cwilsonx100/FPGA-Synthesizer/Synth_V5_sequencer/fpga/Note_to_phase.v

`timescale 1ns / 1ps

//============================================================================
// Note_to_phase
//   MIDI note number -> 32-bit phase increment for the NCO.
//   Computed for Fs = 48000 Hz (clk_audio 12.288 MHz / 256), A4 = 440.000 Hz.
//   phase_inc = round( freq * 2^32 / Fs )
//============================================================================

module Note_to_phase(
    input  wire [6:0]  midi_note,
    output reg  [31:0] phase_inc
);

    always @(*) begin
        case (midi_note)

            7'd0:   phase_inc = 32'd731558;     // C-1   8.176 Hz
            7'd1:   phase_inc = 32'd775059;     // C#-1  8.662 Hz
            7'd2:   phase_inc = 32'd821146;     // D-1   9.177 Hz
            7'd3:   phase_inc = 32'd869974;     // D#-1  9.723 Hz
            7'd4:   phase_inc = 32'd921705;     // E-1   10.301 Hz
            7'd5:   phase_inc = 32'd976513;     // F-1   10.913 Hz
            7'd6:   phase_inc = 32'd1034579;    // F#-1  11.562 Hz
            7'd7:   phase_inc = 32'd1096099;    // G-1   12.250 Hz
            7'd8:   phase_inc = 32'd1161276;    // G#-1  12.978 Hz
            7'd9:   phase_inc = 32'd1230329;    // A-1   13.750 Hz
            7'd10:  phase_inc = 32'd1303488;    // A#-1  14.568 Hz
            7'd11:  phase_inc = 32'd1380998;    // B-1   15.434 Hz

            7'd12:  phase_inc = 32'd1463116;    // C0    16.352 Hz
            7'd13:  phase_inc = 32'd1550118;    // C#0   17.324 Hz
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
            7'd126: phase_inc = 32'd1059409297; // F#9   11839.822 Hz
            7'd127: phase_inc = 32'd1122405052; // G9    12543.854 Hz

            default: phase_inc = 32'd39370534;  // A4 default (440.000 Hz)

        endcase
    end

endmodule
