cwilsonx100/FPGA-Synthesizer/Synth_V5_sequencer/fpga/Wavetable_rom.v

`timescale 1ns / 1ps

//==========================================================================
// Wavetable_rom  -  dual-port block ROM, 7 wavetables x 256 pts.
//   Address = {table_sel[2:0], phase[7:0]}. table_sel = waveform-3:
//     0 = Sine
//     1 = Organ
//     2 = Growl
//     3 = Formant
//     4 = Half Sine
//     5 = Fold
//     6 = Bell
//   (V4.1: redesigned for distinct spectra - replaced Soft Square->Growl,
//    Acid->Fold; all waves now occupy separate harmonic territory.)
//==========================================================================

module Wavetable_rom(
    input  wire        clk,
    input  wire [2:0]  sel_a,  input wire [7:0] phase_a,  output reg signed [15:0] sample_a,
    input  wire [2:0]  sel_b,  input wire [7:0] phase_b,  output reg signed [15:0] sample_b
);

    (* rom_style = "block" *) reg signed [15:0] rom [0:2047];

    integer i;
    initial begin
        for (i=0;i<2048;i=i+1) rom[i]=16'h0000;
        // table 0: Sine
        rom[0]=16'h0000;
        rom[1]=16'h024D;
        rom[2]=16'h049A;
        rom[3]=16'h06E6;
        rom[4]=16'h0930;
        rom[5]=16'h0B7A;
        rom[6]=16'h0DC2;
        rom[7]=16'h1007;
        rom[8]=16'h124A;
        rom[9]=16'h148A;
        rom[10]=16'h16C8;
        rom[11]=16'h1901;
        rom[12]=16'h1B37;
        rom[13]=16'h1D68;
        rom[14]=16'h1F95;
        rom[15]=16'h21BD;
        rom[16]=16'h23E0;
        rom[17]=16'h25FE;
        rom[18]=16'h2815;
        rom[19]=16'h2A27;
        rom[20]=16'h2C32;
        rom[21]=16'h2E36;
        rom[22]=16'h3032;
        rom[23]=16'h3228;
        rom[24]=16'h3416;
        rom[25]=16'h35FB;
        rom[26]=16'h37D9;
        rom[27]=16'h39AE;
        rom[28]=16'h3B79;
        rom[29]=16'h3D3C;
        rom[30]=16'h3EF5;
        rom[31]=16'h40A5;
        rom[32]=16'h424B;
        rom[33]=16'h43E6;
        rom[34]=16'h4577;
        rom[35]=16'h46FD;
        rom[36]=16'h4878;
        rom[37]=16'h49E8;
        rom[38]=16'h4B4D;
        rom[39]=16'h4CA6;
        rom[40]=16'h4DF3;
        rom[41]=16'h4F34;
        rom[42]=16'h5069;
        rom[43]=16'h5192;
        rom[44]=16'h52AE;
        rom[45]=16'h53BD;
        rom[46]=16'h54C0;
        rom[47]=16'h55B5;
        rom[48]=16'h569D;
        rom[49]=16'h5778;
        rom[50]=16'h5845;
        rom[51]=16'h5905;
        rom[52]=16'h59B7;
        rom[53]=16'h5A5B;
        rom[54]=16'h5AF1;
        rom[55]=16'h5B79;
        rom[56]=16'h5BF3;
        rom[57]=16'h5C5F;
        rom[58]=16'h5CBC;
        rom[59]=16'h5D0C;
        rom[60]=16'h5D4C;
        rom[61]=16'h5D7F;
        rom[62]=16'h5DA3;
        rom[63]=16'h5DB9;
        rom[64]=16'h5DC0;
        rom[65]=16'h5DB9;
        rom[66]=16'h5DA3;
        rom[67]=16'h5D7F;
        rom[68]=16'h5D4C;
        rom[69]=16'h5D0C;
        rom[70]=16'h5CBC;
        rom[71]=16'h5C5F;
        rom[72]=16'h5BF3;
        rom[73]=16'h5B79;
        rom[74]=16'h5AF1;
        rom[75]=16'h5A5B;
        rom[76]=16'h59B7;
        rom[77]=16'h5905;
        rom[78]=16'h5845;
        rom[79]=16'h5778;
        rom[80]=16'h569D;
        rom[81]=16'h55B5;
        rom[82]=16'h54C0;
        rom[83]=16'h53BD;
        rom[84]=16'h52AE;
        rom[85]=16'h5192;
        rom[86]=16'h5069;
        rom[87]=16'h4F34;
        rom[88]=16'h4DF3;
        rom[89]=16'h4CA6;
        rom[90]=16'h4B4D;
        rom[91]=16'h49E8;
        rom[92]=16'h4878;
        rom[93]=16'h46FD;
        rom[94]=16'h4577;
        rom[95]=16'h43E6;
        rom[96]=16'h424B;
        rom[97]=16'h40A5;
        rom[98]=16'h3EF5;
        rom[99]=16'h3D3C;
        rom[100]=16'h3B79;
        rom[101]=16'h39AE;
        rom[102]=16'h37D9;
        rom[103]=16'h35FB;
        rom[104]=16'h3416;
        rom[105]=16'h3228;
        rom[106]=16'h3032;
        rom[107]=16'h2E36;
        rom[108]=16'h2C32;
        rom[109]=16'h2A27;
        rom[110]=16'h2815;
        rom[111]=16'h25FE;
        rom[112]=16'h23E0;
        rom[113]=16'h21BD;
        rom[114]=16'h1F95;
        rom[115]=16'h1D68;
        rom[116]=16'h1B37;
        rom[117]=16'h1901;
        rom[118]=16'h16C8;
        rom[119]=16'h148A;
        rom[120]=16'h124A;
        rom[121]=16'h1007;
        rom[122]=16'h0DC2;
        rom[123]=16'h0B7A;
        rom[124]=16'h0930;
        rom[125]=16'h06E6;
        rom[126]=16'h049A;
        rom[127]=16'h024D;
        rom[128]=16'h0000;
        rom[129]=16'hFDB3;
        rom[130]=16'hFB66;
        rom[131]=16'hF91A;
        rom[132]=16'hF6D0;
        rom[133]=16'hF486;
        rom[134]=16'hF23E;
        rom[135]=16'hEFF9;
        rom[136]=16'hEDB6;
        rom[137]=16'hEB76;
        rom[138]=16'hE938;
        rom[139]=16'hE6FF;
        rom[140]=16'hE4C9;
        rom[141]=16'hE298;
        rom[142]=16'hE06B;
        rom[143]=16'hDE43;
        rom[144]=16'hDC20;
        rom[145]=16'hDA02;
        rom[146]=16'hD7EB;
        rom[147]=16'hD5D9;
        rom[148]=16'hD3CE;
        rom[149]=16'hD1CA;
        rom[150]=16'hCFCE;
        rom[151]=16'hCDD8;
        rom[152]=16'hCBEA;
        rom[153]=16'hCA05;
        rom[154]=16'hC827;
        rom[155]=16'hC652;
        rom[156]=16'hC487;
        rom[157]=16'hC2C4;
        rom[158]=16'hC10B;
        rom[159]=16'hBF5B;
        rom[160]=16'hBDB5;
        rom[161]=16'hBC1A;
        rom[162]=16'hBA89;
        rom[163]=16'hB903;
        rom[164]=16'hB788;
        rom[165]=16'hB618;
        rom[166]=16'hB4B3;
        rom[167]=16'hB35A;
        rom[168]=16'hB20D;
        rom[169]=16'hB0CC;
        rom[170]=16'hAF97;
        rom[171]=16'hAE6E;
        rom[172]=16'hAD52;
        rom[173]=16'hAC43;
        rom[174]=16'hAB40;
        rom[175]=16'hAA4B;
        rom[176]=16'hA963;
        rom[177]=16'hA888;
        rom[178]=16'hA7BB;
        rom[179]=16'hA6FB;
        rom[180]=16'hA649;
        rom[181]=16'hA5A5;
        rom[182]=16'hA50F;
        rom[183]=16'hA487;
        rom[184]=16'hA40D;
        rom[185]=16'hA3A1;
        rom[186]=16'hA344;
        rom[187]=16'hA2F4;
        rom[188]=16'hA2B4;
        rom[189]=16'hA281;
        rom[190]=16'hA25D;
        rom[191]=16'hA247;
        rom[192]=16'hA240;
        rom[193]=16'hA247;
        rom[194]=16'hA25D;
        rom[195]=16'hA281;
        rom[196]=16'hA2B4;
        rom[197]=16'hA2F4;
        rom[198]=16'hA344;
        rom[199]=16'hA3A1;
        rom[200]=16'hA40D;
        rom[201]=16'hA487;
        rom[202]=16'hA50F;
        rom[203]=16'hA5A5;
        rom[204]=16'hA649;
        rom[205]=16'hA6FB;
        rom[206]=16'hA7BB;
        rom[207]=16'hA888;
        rom[208]=16'hA963;
        rom[209]=16'hAA4B;
        rom[210]=16'hAB40;
        rom[211]=16'hAC43;
        rom[212]=16'hAD52;
        rom[213]=16'hAE6E;
        rom[214]=16'hAF97;
        rom[215]=16'hB0CC;
        rom[216]=16'hB20D;
        rom[217]=16'hB35A;
        rom[218]=16'hB4B3;
        rom[219]=16'hB618;
        rom[220]=16'hB788;
        rom[221]=16'hB903;
        rom[222]=16'hBA89;
        rom[223]=16'hBC1A;
        rom[224]=16'hBDB5;
        rom[225]=16'hBF5B;
        rom[226]=16'hC10B;
        rom[227]=16'hC2C4;
        rom[228]=16'hC487;
        rom[229]=16'hC652;
        rom[230]=16'hC827;
        rom[231]=16'hCA05;
        rom[232]=16'hCBEA;
        rom[233]=16'hCDD8;
        rom[234]=16'hCFCE;
        rom[235]=16'hD1CA;
        rom[236]=16'hD3CE;
        rom[237]=16'hD5D9;
        rom[238]=16'hD7EB;
        rom[239]=16'hDA02;
        rom[240]=16'hDC20;
        rom[241]=16'hDE43;
        rom[242]=16'hE06B;
        rom[243]=16'hE298;
        rom[244]=16'hE4C9;
        rom[245]=16'hE6FF;
        rom[246]=16'hE938;
        rom[247]=16'hEB76;
        rom[248]=16'hEDB6;
        rom[249]=16'hEFF9;
        rom[250]=16'hF23E;
        rom[251]=16'hF486;
        rom[252]=16'hF6D0;
        rom[253]=16'hF91A;
        rom[254]=16'hFB66;
        rom[255]=16'hFDB3;
        // table 1: Organ
        rom[256]=16'h0000;
        rom[257]=16'h0E65;
        rom[258]=16'h1BDE;
        rom[259]=16'h27A0;
        rom[260]=16'h3114;
        rom[261]=16'h37F0;
        rom[262]=16'h3C3A;
        rom[263]=16'h3E44;
        rom[264]=16'h3E9D;
        rom[265]=16'h3DF8;
        rom[266]=16'h3D10;
        rom[267]=16'h3C8C;
        rom[268]=16'h3CE5;
        rom[269]=16'h3E56;
        rom[270]=16'h40D4;
        rom[271]=16'h4415;
        rom[272]=16'h479A;
        rom[273]=16'h4ACD;
        rom[274]=16'h4D18;
        rom[275]=16'h4DFF;
        rom[276]=16'h4D3B;
        rom[277]=16'h4AC5;
        rom[278]=16'h46DE;
        rom[279]=16'h4205;
        rom[280]=16'h3CE9;
        rom[281]=16'h384E;
        rom[282]=16'h34F2;
        rom[283]=16'h336D;
        rom[284]=16'h341E;
        rom[285]=16'h3715;
        rom[286]=16'h3C14;
        rom[287]=16'h4295;
        rom[288]=16'h49D6;
        rom[289]=16'h50FA;
        rom[290]=16'h5724;
        rom[291]=16'h5B93;
        rom[292]=16'h5DC0;
        rom[293]=16'h5D6D;
        rom[294]=16'h5AAD;
        rom[295]=16'h55DE;
        rom[296]=16'h4F99;
        rom[297]=16'h489D;
        rom[298]=16'h41AF;
        rom[299]=16'h3B7E;
        rom[300]=16'h368C;
        rom[301]=16'h3319;
        rom[302]=16'h3123;
        rom[303]=16'h3061;
        rom[304]=16'h305A;
        rom[305]=16'h307B;
        rom[306]=16'h302C;
        rom[307]=16'h2EF4;
        rom[308]=16'h2C88;
        rom[309]=16'h28E2;
        rom[310]=16'h243C;
        rom[311]=16'h1F13;
        rom[312]=16'h1A0F;
        rom[313]=16'h15EE;
        rom[314]=16'h1365;
        rom[315]=16'h1307;
        rom[316]=16'h1526;
        rom[317]=16'h19CB;
        rom[318]=16'h20AE;
        rom[319]=16'h293D;
        rom[320]=16'h32AC;
        rom[321]=16'h3C14;
        rom[322]=16'h448B;
        rom[323]=16'h4B47;
        rom[324]=16'h4FB6;
        rom[325]=16'h518F;
        rom[326]=16'h50DA;
        rom[327]=16'h4DED;
        rom[328]=16'h4957;
        rom[329]=16'h43CF;
        rom[330]=16'h3E13;
        rom[331]=16'h38CB;
        rom[332]=16'h3473;
        rom[333]=16'h3147;
        rom[334]=16'h2F40;
        rom[335]=16'h2E13;
        rom[336]=16'h2D47;
        rom[337]=16'h2C46;
        rom[338]=16'h2A7B;
        rom[339]=16'h276D;
        rom[340]=16'h22D5;
        rom[341]=16'h1CB0;
        rom[342]=16'h153F;
        rom[343]=16'h0D02;
        rom[344]=16'h04AB;
        rom[345]=16'hFCFE;
        rom[346]=16'hF6BA;
        rom[347]=16'hF278;
        rom[348]=16'hF097;
        rom[349]=16'hF12B;
        rom[350]=16'hF3F4;
        rom[351]=16'hF86C;
        rom[352]=16'hFDD4;
        rom[353]=16'h034D;
        rom[354]=16'h07FB;
        rom[355]=16'h0B1D;
        rom[356]=16'h0C2D;
        rom[357]=16'h0AEC;
        rom[358]=16'h076D;
        rom[359]=16'h020D;
        rom[360]=16'hFB65;
        rom[361]=16'hF433;
        rom[362]=16'hED3C;
        rom[363]=16'hE72F;
        rom[364]=16'hE28B;
        rom[365]=16'hDF92;
        rom[366]=16'hDE3D;
        rom[367]=16'hDE44;
        rom[368]=16'hDF2F;
        rom[369]=16'hE065;
        rom[370]=16'hE150;
        rom[371]=16'hE174;
        rom[372]=16'hE086;
        rom[373]=16'hDE7C;
        rom[374]=16'hDB90;
        rom[375]=16'hD83C;
        rom[376]=16'hD528;
        rom[377]=16'hD30F;
        rom[378]=16'hD2A5;
        rom[379]=16'hD478;
        rom[380]=16'hD8DB;
        rom[381]=16'hDFD5;
        rom[382]=16'hE91B;
        rom[383]=16'hF418;
        rom[384]=16'h0000;
        rom[385]=16'h0BE8;
        rom[386]=16'h16E5;
        rom[387]=16'h202B;
        rom[388]=16'h2725;
        rom[389]=16'h2B88;
        rom[390]=16'h2D5B;
        rom[391]=16'h2CF1;
        rom[392]=16'h2AD8;
        rom[393]=16'h27C4;
        rom[394]=16'h2470;
        rom[395]=16'h2184;
        rom[396]=16'h1F7A;
        rom[397]=16'h1E8C;
        rom[398]=16'h1EB0;
        rom[399]=16'h1F9B;
        rom[400]=16'h20D1;
        rom[401]=16'h21BC;
        rom[402]=16'h21C3;
        rom[403]=16'h206E;
        rom[404]=16'h1D75;
        rom[405]=16'h18D1;
        rom[406]=16'h12C4;
        rom[407]=16'h0BCD;
        rom[408]=16'h049B;
        rom[409]=16'hFDF3;
        rom[410]=16'hF893;
        rom[411]=16'hF514;
        rom[412]=16'hF3D3;
        rom[413]=16'hF4E3;
        rom[414]=16'hF805;
        rom[415]=16'hFCB3;
        rom[416]=16'h022C;
        rom[417]=16'h0794;
        rom[418]=16'h0C0C;
        rom[419]=16'h0ED5;
        rom[420]=16'h0F69;
        rom[421]=16'h0D88;
        rom[422]=16'h0946;
        rom[423]=16'h0302;
        rom[424]=16'hFB55;
        rom[425]=16'hF2FE;
        rom[426]=16'hEAC1;
        rom[427]=16'hE350;
        rom[428]=16'hDD2B;
        rom[429]=16'hD893;
        rom[430]=16'hD585;
        rom[431]=16'hD3BA;
        rom[432]=16'hD2B9;
        rom[433]=16'hD1ED;
        rom[434]=16'hD0C0;
        rom[435]=16'hCEB9;
        rom[436]=16'hCB8D;
        rom[437]=16'hC735;
        rom[438]=16'hC1ED;
        rom[439]=16'hBC31;
        rom[440]=16'hB6A9;
        rom[441]=16'hB213;
        rom[442]=16'hAF26;
        rom[443]=16'hAE71;
        rom[444]=16'hB04A;
        rom[445]=16'hB4B9;
        rom[446]=16'hBB75;
        rom[447]=16'hC3EC;
        rom[448]=16'hCD54;
        rom[449]=16'hD6C3;
        rom[450]=16'hDF52;
        rom[451]=16'hE635;
        rom[452]=16'hEADA;
        rom[453]=16'hECF9;
        rom[454]=16'hEC9B;
        rom[455]=16'hEA12;
        rom[456]=16'hE5F1;
        rom[457]=16'hE0ED;
        rom[458]=16'hDBC4;
        rom[459]=16'hD71E;
        rom[460]=16'hD378;
        rom[461]=16'hD10C;
        rom[462]=16'hCFD4;
        rom[463]=16'hCF85;
        rom[464]=16'hCFA6;
        rom[465]=16'hCF9F;
        rom[466]=16'hCEDD;
        rom[467]=16'hCCE7;
        rom[468]=16'hC974;
        rom[469]=16'hC482;
        rom[470]=16'hBE51;
        rom[471]=16'hB763;
        rom[472]=16'hB067;
        rom[473]=16'hAA22;
        rom[474]=16'hA553;
        rom[475]=16'hA293;
        rom[476]=16'hA240;
        rom[477]=16'hA46D;
        rom[478]=16'hA8DC;
        rom[479]=16'hAF06;
        rom[480]=16'hB62A;
        rom[481]=16'hBD6B;
        rom[482]=16'hC3EC;
        rom[483]=16'hC8EB;
        rom[484]=16'hCBE2;
        rom[485]=16'hCC93;
        rom[486]=16'hCB0E;
        rom[487]=16'hC7B2;
        rom[488]=16'hC317;
        rom[489]=16'hBDFB;
        rom[490]=16'hB922;
        rom[491]=16'hB53B;
        rom[492]=16'hB2C5;
        rom[493]=16'hB201;
        rom[494]=16'hB2E8;
        rom[495]=16'hB533;
        rom[496]=16'hB866;
        rom[497]=16'hBBEB;
        rom[498]=16'hBF2C;
        rom[499]=16'hC1AA;
        rom[500]=16'hC31B;
        rom[501]=16'hC374;
        rom[502]=16'hC2F0;
        rom[503]=16'hC208;
        rom[504]=16'hC163;
        rom[505]=16'hC1BC;
        rom[506]=16'hC3C6;
        rom[507]=16'hC810;
        rom[508]=16'hCEEC;
        rom[509]=16'hD860;
        rom[510]=16'hE422;
        rom[511]=16'hF19B;
        // table 2: Growl
        rom[512]=16'h381B;
        rom[513]=16'h364E;
        rom[514]=16'h3496;
        rom[515]=16'h32F7;
        rom[516]=16'h3170;
        rom[517]=16'h3003;
        rom[518]=16'h2EB2;
        rom[519]=16'h2D7D;
        rom[520]=16'h2C64;
        rom[521]=16'h2B69;
        rom[522]=16'h2A8C;
        rom[523]=16'h29CD;
        rom[524]=16'h292D;
        rom[525]=16'h28AB;
        rom[526]=16'h2848;
        rom[527]=16'h2803;
        rom[528]=16'h27DD;
        rom[529]=16'h27D5;
        rom[530]=16'h27EB;
        rom[531]=16'h281E;
        rom[532]=16'h286F;
        rom[533]=16'h28DC;
        rom[534]=16'h2965;
        rom[535]=16'h2A09;
        rom[536]=16'h2AC8;
        rom[537]=16'h2BA1;
        rom[538]=16'h2C92;
        rom[539]=16'h2D9B;
        rom[540]=16'h2EBB;
        rom[541]=16'h2FF1;
        rom[542]=16'h313C;
        rom[543]=16'h329A;
        rom[544]=16'h3409;
        rom[545]=16'h3589;
        rom[546]=16'h3719;
        rom[547]=16'h38B5;
        rom[548]=16'h3A5E;
        rom[549]=16'h3C11;
        rom[550]=16'h3DCC;
        rom[551]=16'h3F8D;
        rom[552]=16'h4153;
        rom[553]=16'h431C;
        rom[554]=16'h44E5;
        rom[555]=16'h46AD;
        rom[556]=16'h4872;
        rom[557]=16'h4A32;
        rom[558]=16'h4BEA;
        rom[559]=16'h4D98;
        rom[560]=16'h4F3B;
        rom[561]=16'h50D0;
        rom[562]=16'h5256;
        rom[563]=16'h53CA;
        rom[564]=16'h552B;
        rom[565]=16'h5677;
        rom[566]=16'h57AC;
        rom[567]=16'h58C9;
        rom[568]=16'h59CC;
        rom[569]=16'h5AB4;
        rom[570]=16'h5B80;
        rom[571]=16'h5C2E;
        rom[572]=16'h5CBE;
        rom[573]=16'h5D2E;
        rom[574]=16'h5D7F;
        rom[575]=16'h5DB0;
        rom[576]=16'h5DC0;
        rom[577]=16'h5DB0;
        rom[578]=16'h5D7F;
        rom[579]=16'h5D2E;
        rom[580]=16'h5CBE;
        rom[581]=16'h5C2E;
        rom[582]=16'h5B80;
        rom[583]=16'h5AB4;
        rom[584]=16'h59CC;
        rom[585]=16'h58C9;
        rom[586]=16'h57AC;
        rom[587]=16'h5677;
        rom[588]=16'h552B;
        rom[589]=16'h53CA;
        rom[590]=16'h5256;
        rom[591]=16'h50D0;
        rom[592]=16'h4F3B;
        rom[593]=16'h4D98;
        rom[594]=16'h4BEA;
        rom[595]=16'h4A32;
        rom[596]=16'h4872;
        rom[597]=16'h46AD;
        rom[598]=16'h44E5;
        rom[599]=16'h431C;
        rom[600]=16'h4153;
        rom[601]=16'h3F8D;
        rom[602]=16'h3DCC;
        rom[603]=16'h3C11;
        rom[604]=16'h3A5E;
        rom[605]=16'h38B5;
        rom[606]=16'h3719;
        rom[607]=16'h3589;
        rom[608]=16'h3409;
        rom[609]=16'h329A;
        rom[610]=16'h313C;
        rom[611]=16'h2FF1;
        rom[612]=16'h2EBB;
        rom[613]=16'h2D9B;
        rom[614]=16'h2C92;
        rom[615]=16'h2BA1;
        rom[616]=16'h2AC8;
        rom[617]=16'h2A09;
        rom[618]=16'h2965;
        rom[619]=16'h28DC;
        rom[620]=16'h286F;
        rom[621]=16'h281E;
        rom[622]=16'h27EB;
        rom[623]=16'h27D5;
        rom[624]=16'h27DD;
        rom[625]=16'h2803;
        rom[626]=16'h2848;
        rom[627]=16'h28AB;
        rom[628]=16'h292D;
        rom[629]=16'h29CD;
        rom[630]=16'h2A8C;
        rom[631]=16'h2B69;
        rom[632]=16'h2C64;
        rom[633]=16'h2D7D;
        rom[634]=16'h2EB2;
        rom[635]=16'h3003;
        rom[636]=16'h3170;
        rom[637]=16'h32F7;
        rom[638]=16'h3496;
        rom[639]=16'h364E;
        rom[640]=16'h381B;
        rom[641]=16'h39FD;
        rom[642]=16'h3BF1;
        rom[643]=16'h3DF5;
        rom[644]=16'h4007;
        rom[645]=16'h4224;
        rom[646]=16'h4448;
        rom[647]=16'h4672;
        rom[648]=16'h489D;
        rom[649]=16'h4AC5;
        rom[650]=16'h4CE7;
        rom[651]=16'h4EFF;
        rom[652]=16'h5107;
        rom[653]=16'h52FC;
        rom[654]=16'h54D8;
        rom[655]=16'h5695;
        rom[656]=16'h5830;
        rom[657]=16'h59A2;
        rom[658]=16'h5AE5;
        rom[659]=16'h5BF5;
        rom[660]=16'h5CCB;
        rom[661]=16'h5D61;
        rom[662]=16'h5DB2;
        rom[663]=16'h5DBA;
        rom[664]=16'h5D71;
        rom[665]=16'h5CD4;
        rom[666]=16'h5BDD;
        rom[667]=16'h5A89;
        rom[668]=16'h58D4;
        rom[669]=16'h56BA;
        rom[670]=16'h5439;
        rom[671]=16'h514F;
        rom[672]=16'h4DFC;
        rom[673]=16'h4A3E;
        rom[674]=16'h4616;
        rom[675]=16'h4186;
        rom[676]=16'h3C91;
        rom[677]=16'h373B;
        rom[678]=16'h3187;
        rom[679]=16'h2B7C;
        rom[680]=16'h2520;
        rom[681]=16'h1E7C;
        rom[682]=16'h1798;
        rom[683]=16'h107F;
        rom[684]=16'h093A;
        rom[685]=16'h01D5;
        rom[686]=16'hFA5E;
        rom[687]=16'hF2E0;
        rom[688]=16'hEB6A;
        rom[689]=16'hE409;
        rom[690]=16'hDCCB;
        rom[691]=16'hD5C0;
        rom[692]=16'hCEF4;
        rom[693]=16'hC876;
        rom[694]=16'hC255;
        rom[695]=16'hBC9C;
        rom[696]=16'hB758;
        rom[697]=16'hB295;
        rom[698]=16'hAE5E;
        rom[699]=16'hAABC;
        rom[700]=16'hA7B8;
        rom[701]=16'hA558;
        rom[702]=16'hA3A1;
        rom[703]=16'hA298;
        rom[704]=16'hA240;
        rom[705]=16'hA298;
        rom[706]=16'hA3A1;
        rom[707]=16'hA558;
        rom[708]=16'hA7B8;
        rom[709]=16'hAABC;
        rom[710]=16'hAE5E;
        rom[711]=16'hB295;
        rom[712]=16'hB758;
        rom[713]=16'hBC9C;
        rom[714]=16'hC255;
        rom[715]=16'hC876;
        rom[716]=16'hCEF4;
        rom[717]=16'hD5C0;
        rom[718]=16'hDCCB;
        rom[719]=16'hE409;
        rom[720]=16'hEB6A;
        rom[721]=16'hF2E0;
        rom[722]=16'hFA5E;
        rom[723]=16'h01D5;
        rom[724]=16'h093A;
        rom[725]=16'h107F;
        rom[726]=16'h1798;
        rom[727]=16'h1E7C;
        rom[728]=16'h2520;
        rom[729]=16'h2B7C;
        rom[730]=16'h3187;
        rom[731]=16'h373B;
        rom[732]=16'h3C91;
        rom[733]=16'h4186;
        rom[734]=16'h4616;
        rom[735]=16'h4A3E;
        rom[736]=16'h4DFC;
        rom[737]=16'h514F;
        rom[738]=16'h5439;
        rom[739]=16'h56BA;
        rom[740]=16'h58D4;
        rom[741]=16'h5A89;
        rom[742]=16'h5BDD;
        rom[743]=16'h5CD4;
        rom[744]=16'h5D71;
        rom[745]=16'h5DBA;
        rom[746]=16'h5DB2;
        rom[747]=16'h5D61;
        rom[748]=16'h5CCB;
        rom[749]=16'h5BF5;
        rom[750]=16'h5AE5;
        rom[751]=16'h59A2;
        rom[752]=16'h5830;
        rom[753]=16'h5695;
        rom[754]=16'h54D8;
        rom[755]=16'h52FC;
        rom[756]=16'h5107;
        rom[757]=16'h4EFF;
        rom[758]=16'h4CE7;
        rom[759]=16'h4AC5;
        rom[760]=16'h489D;
        rom[761]=16'h4672;
        rom[762]=16'h4448;
        rom[763]=16'h4224;
        rom[764]=16'h4007;
        rom[765]=16'h3DF5;
        rom[766]=16'h3BF1;
        rom[767]=16'h39FD;
        // table 3: Formant
        rom[768]=16'h0000;
        rom[769]=16'h0AED;
        rom[770]=16'h15B3;
        rom[771]=16'h202D;
        rom[772]=16'h2A35;
        rom[773]=16'h33A8;
        rom[774]=16'h3C65;
        rom[775]=16'h444F;
        rom[776]=16'h4B4A;
        rom[777]=16'h5140;
        rom[778]=16'h561E;
        rom[779]=16'h59D5;
        rom[780]=16'h5C5A;
        rom[781]=16'h5DA9;
        rom[782]=16'h5DC0;
        rom[783]=16'h5CA3;
        rom[784]=16'h5A5B;
        rom[785]=16'h56F3;
        rom[786]=16'h527D;
        rom[787]=16'h4D0E;
        rom[788]=16'h46BE;
        rom[789]=16'h3FA6;
        rom[790]=16'h37E7;
        rom[791]=16'h2F9E;
        rom[792]=16'h26ED;
        rom[793]=16'h1DF6;
        rom[794]=16'h14DD;
        rom[795]=16'h0BC3;
        rom[796]=16'h02CB;
        rom[797]=16'hFA15;
        rom[798]=16'hF1BF;
        rom[799]=16'hE9E8;
        rom[800]=16'hE2A9;
        rom[801]=16'hDC1A;
        rom[802]=16'hD64F;
        rom[803]=16'hD159;
        rom[804]=16'hCD45;
        rom[805]=16'hCA1C;
        rom[806]=16'hC7E5;
        rom[807]=16'hC6A0;
        rom[808]=16'hC64D;
        rom[809]=16'hC6E5;
        rom[810]=16'hC85F;
        rom[811]=16'hCAB1;
        rom[812]=16'hCDCB;
        rom[813]=16'hD19C;
        rom[814]=16'hD60F;
        rom[815]=16'hDB11;
        rom[816]=16'hE08A;
        rom[817]=16'hE663;
        rom[818]=16'hEC83;
        rom[819]=16'hF2D3;
        rom[820]=16'hF93B;
        rom[821]=16'hFFA2;
        rom[822]=16'h05F4;
        rom[823]=16'h0C1A;
        rom[824]=16'h1201;
        rom[825]=16'h1799;
        rom[826]=16'h1CD1;
        rom[827]=16'h219C;
        rom[828]=16'h25F0;
        rom[829]=16'h29C3;
        rom[830]=16'h2D10;
        rom[831]=16'h2FD3;
        rom[832]=16'h320A;
        rom[833]=16'h33B7;
        rom[834]=16'h34DC;
        rom[835]=16'h357E;
        rom[836]=16'h35A2;
        rom[837]=16'h3552;
        rom[838]=16'h3496;
        rom[839]=16'h3378;
        rom[840]=16'h3203;
        rom[841]=16'h3041;
        rom[842]=16'h2E3F;
        rom[843]=16'h2C08;
        rom[844]=16'h29A7;
        rom[845]=16'h2727;
        rom[846]=16'h2492;
        rom[847]=16'h21F1;
        rom[848]=16'h1F4D;
        rom[849]=16'h1CAD;
        rom[850]=16'h1A19;
        rom[851]=16'h1795;
        rom[852]=16'h1527;
        rom[853]=16'h12D0;
        rom[854]=16'h1094;
        rom[855]=16'h0E75;
        rom[856]=16'h0C71;
        rom[857]=16'h0A8B;
        rom[858]=16'h08BF;
        rom[859]=16'h070E;
        rom[860]=16'h0575;
        rom[861]=16'h03F2;
        rom[862]=16'h0284;
        rom[863]=16'h0127;
        rom[864]=16'hFFDA;
        rom[865]=16'hFE9B;
        rom[866]=16'hFD69;
        rom[867]=16'hFC42;
        rom[868]=16'hFB26;
        rom[869]=16'hFA14;
        rom[870]=16'hF90C;
        rom[871]=16'hF80F;
        rom[872]=16'hF71F;
        rom[873]=16'hF63D;
        rom[874]=16'hF56B;
        rom[875]=16'hF4AA;
        rom[876]=16'hF3FE;
        rom[877]=16'hF369;
        rom[878]=16'hF2EE;
        rom[879]=16'hF290;
        rom[880]=16'hF250;
        rom[881]=16'hF231;
        rom[882]=16'hF235;
        rom[883]=16'hF25E;
        rom[884]=16'hF2AC;
        rom[885]=16'hF31F;
        rom[886]=16'hF3B9;
        rom[887]=16'hF477;
        rom[888]=16'hF559;
        rom[889]=16'hF65D;
        rom[890]=16'hF77F;
        rom[891]=16'hF8BD;
        rom[892]=16'hFA13;
        rom[893]=16'hFB7C;
        rom[894]=16'hFCF5;
        rom[895]=16'hFE78;
        rom[896]=16'h0000;
        rom[897]=16'h0188;
        rom[898]=16'h030B;
        rom[899]=16'h0484;
        rom[900]=16'h05ED;
        rom[901]=16'h0743;
        rom[902]=16'h0881;
        rom[903]=16'h09A3;
        rom[904]=16'h0AA7;
        rom[905]=16'h0B89;
        rom[906]=16'h0C47;
        rom[907]=16'h0CE1;
        rom[908]=16'h0D54;
        rom[909]=16'h0DA2;
        rom[910]=16'h0DCB;
        rom[911]=16'h0DCF;
        rom[912]=16'h0DB0;
        rom[913]=16'h0D70;
        rom[914]=16'h0D12;
        rom[915]=16'h0C97;
        rom[916]=16'h0C02;
        rom[917]=16'h0B56;
        rom[918]=16'h0A95;
        rom[919]=16'h09C3;
        rom[920]=16'h08E1;
        rom[921]=16'h07F1;
        rom[922]=16'h06F4;
        rom[923]=16'h05EC;
        rom[924]=16'h04DA;
        rom[925]=16'h03BE;
        rom[926]=16'h0297;
        rom[927]=16'h0165;
        rom[928]=16'h0026;
        rom[929]=16'hFED9;
        rom[930]=16'hFD7C;
        rom[931]=16'hFC0E;
        rom[932]=16'hFA8B;
        rom[933]=16'hF8F2;
        rom[934]=16'hF741;
        rom[935]=16'hF575;
        rom[936]=16'hF38F;
        rom[937]=16'hF18B;
        rom[938]=16'hEF6C;
        rom[939]=16'hED30;
        rom[940]=16'hEAD9;
        rom[941]=16'hE86B;
        rom[942]=16'hE5E7;
        rom[943]=16'hE353;
        rom[944]=16'hE0B3;
        rom[945]=16'hDE0F;
        rom[946]=16'hDB6E;
        rom[947]=16'hD8D9;
        rom[948]=16'hD659;
        rom[949]=16'hD3F8;
        rom[950]=16'hD1C1;
        rom[951]=16'hCFBF;
        rom[952]=16'hCDFD;
        rom[953]=16'hCC88;
        rom[954]=16'hCB6A;
        rom[955]=16'hCAAE;
        rom[956]=16'hCA5E;
        rom[957]=16'hCA82;
        rom[958]=16'hCB24;
        rom[959]=16'hCC49;
        rom[960]=16'hCDF6;
        rom[961]=16'hD02D;
        rom[962]=16'hD2F0;
        rom[963]=16'hD63D;
        rom[964]=16'hDA10;
        rom[965]=16'hDE64;
        rom[966]=16'hE32F;
        rom[967]=16'hE867;
        rom[968]=16'hEDFF;
        rom[969]=16'hF3E6;
        rom[970]=16'hFA0C;
        rom[971]=16'h005E;
        rom[972]=16'h06C5;
        rom[973]=16'h0D2D;
        rom[974]=16'h137D;
        rom[975]=16'h199D;
        rom[976]=16'h1F76;
        rom[977]=16'h24EF;
        rom[978]=16'h29F1;
        rom[979]=16'h2E64;
        rom[980]=16'h3235;
        rom[981]=16'h354F;
        rom[982]=16'h37A1;
        rom[983]=16'h391B;
        rom[984]=16'h39B3;
        rom[985]=16'h3960;
        rom[986]=16'h381B;
        rom[987]=16'h35E4;
        rom[988]=16'h32BB;
        rom[989]=16'h2EA7;
        rom[990]=16'h29B1;
        rom[991]=16'h23E6;
        rom[992]=16'h1D57;
        rom[993]=16'h1618;
        rom[994]=16'h0E41;
        rom[995]=16'h05EB;
        rom[996]=16'hFD35;
        rom[997]=16'hF43D;
        rom[998]=16'hEB23;
        rom[999]=16'hE20A;
        rom[1000]=16'hD913;
        rom[1001]=16'hD062;
        rom[1002]=16'hC819;
        rom[1003]=16'hC05A;
        rom[1004]=16'hB942;
        rom[1005]=16'hB2F2;
        rom[1006]=16'hAD83;
        rom[1007]=16'hA90D;
        rom[1008]=16'hA5A5;
        rom[1009]=16'hA35D;
        rom[1010]=16'hA240;
        rom[1011]=16'hA257;
        rom[1012]=16'hA3A6;
        rom[1013]=16'hA62B;
        rom[1014]=16'hA9E2;
        rom[1015]=16'hAEC0;
        rom[1016]=16'hB4B6;
        rom[1017]=16'hBBB1;
        rom[1018]=16'hC39B;
        rom[1019]=16'hCC58;
        rom[1020]=16'hD5CB;
        rom[1021]=16'hDFD3;
        rom[1022]=16'hEA4D;
        rom[1023]=16'hF513;
        // table 4: Half Sine
        rom[1024]=16'hA240;
        rom[1025]=16'hA5DD;
        rom[1026]=16'hA97A;
        rom[1027]=16'hAD15;
        rom[1028]=16'hB0AF;
        rom[1029]=16'hB447;
        rom[1030]=16'hB7DC;
        rom[1031]=16'hBB6D;
        rom[1032]=16'hBEFB;
        rom[1033]=16'hC284;
        rom[1034]=16'hC608;
        rom[1035]=16'hC987;
        rom[1036]=16'hCD00;
        rom[1037]=16'hD072;
        rom[1038]=16'hD3DD;
        rom[1039]=16'hD740;
        rom[1040]=16'hDA9B;
        rom[1041]=16'hDDEE;
        rom[1042]=16'hE137;
        rom[1043]=16'hE476;
        rom[1044]=16'hE7AC;
        rom[1045]=16'hEAD6;
        rom[1046]=16'hEDF6;
        rom[1047]=16'hF10A;
        rom[1048]=16'hF411;
        rom[1049]=16'hF70C;
        rom[1050]=16'hF9FA;
        rom[1051]=16'hFCDA;
        rom[1052]=16'hFFAD;
        rom[1053]=16'h0271;
        rom[1054]=16'h0526;
        rom[1055]=16'h07CC;
        rom[1056]=16'h0A62;
        rom[1057]=16'h0CE8;
        rom[1058]=16'h0F5E;
        rom[1059]=16'h11C3;
        rom[1060]=16'h1417;
        rom[1061]=16'h1659;
        rom[1062]=16'h1889;
        rom[1063]=16'h1AA7;
        rom[1064]=16'h1CB3;
        rom[1065]=16'h1EAB;
        rom[1066]=16'h2091;
        rom[1067]=16'h2263;
        rom[1068]=16'h2421;
        rom[1069]=16'h25CB;
        rom[1070]=16'h2761;
        rom[1071]=16'h28E2;
        rom[1072]=16'h2A4F;
        rom[1073]=16'h2BA6;
        rom[1074]=16'h2CE8;
        rom[1075]=16'h2E15;
        rom[1076]=16'h2F2D;
        rom[1077]=16'h302F;
        rom[1078]=16'h311A;
        rom[1079]=16'h31F0;
        rom[1080]=16'h32B0;
        rom[1081]=16'h3359;
        rom[1082]=16'h33EC;
        rom[1083]=16'h3469;
        rom[1084]=16'h34CF;
        rom[1085]=16'h351E;
        rom[1086]=16'h3557;
        rom[1087]=16'h3579;
        rom[1088]=16'h3584;
        rom[1089]=16'h3579;
        rom[1090]=16'h3557;
        rom[1091]=16'h351E;
        rom[1092]=16'h34CF;
        rom[1093]=16'h3469;
        rom[1094]=16'h33EC;
        rom[1095]=16'h3359;
        rom[1096]=16'h32B0;
        rom[1097]=16'h31F0;
        rom[1098]=16'h311A;
        rom[1099]=16'h302F;
        rom[1100]=16'h2F2D;
        rom[1101]=16'h2E15;
        rom[1102]=16'h2CE8;
        rom[1103]=16'h2BA6;
        rom[1104]=16'h2A4F;
        rom[1105]=16'h28E2;
        rom[1106]=16'h2761;
        rom[1107]=16'h25CB;
        rom[1108]=16'h2421;
        rom[1109]=16'h2263;
        rom[1110]=16'h2091;
        rom[1111]=16'h1EAB;
        rom[1112]=16'h1CB3;
        rom[1113]=16'h1AA7;
        rom[1114]=16'h1889;
        rom[1115]=16'h1659;
        rom[1116]=16'h1417;
        rom[1117]=16'h11C3;
        rom[1118]=16'h0F5E;
        rom[1119]=16'h0CE8;
        rom[1120]=16'h0A62;
        rom[1121]=16'h07CC;
        rom[1122]=16'h0526;
        rom[1123]=16'h0271;
        rom[1124]=16'hFFAD;
        rom[1125]=16'hFCDA;
        rom[1126]=16'hF9FA;
        rom[1127]=16'hF70C;
        rom[1128]=16'hF411;
        rom[1129]=16'hF10A;
        rom[1130]=16'hEDF6;
        rom[1131]=16'hEAD6;
        rom[1132]=16'hE7AC;
        rom[1133]=16'hE476;
        rom[1134]=16'hE137;
        rom[1135]=16'hDDEE;
        rom[1136]=16'hDA9B;
        rom[1137]=16'hD740;
        rom[1138]=16'hD3DD;
        rom[1139]=16'hD072;
        rom[1140]=16'hCD00;
        rom[1141]=16'hC987;
        rom[1142]=16'hC608;
        rom[1143]=16'hC284;
        rom[1144]=16'hBEFB;
        rom[1145]=16'hBB6D;
        rom[1146]=16'hB7DC;
        rom[1147]=16'hB447;
        rom[1148]=16'hB0AF;
        rom[1149]=16'hAD15;
        rom[1150]=16'hA97A;
        rom[1151]=16'hA5DD;
        rom[1152]=16'hA240;
        rom[1153]=16'hA5DD;
        rom[1154]=16'hA97A;
        rom[1155]=16'hAD15;
        rom[1156]=16'hB0AF;
        rom[1157]=16'hB447;
        rom[1158]=16'hB7DC;
        rom[1159]=16'hBB6D;
        rom[1160]=16'hBEFB;
        rom[1161]=16'hC284;
        rom[1162]=16'hC608;
        rom[1163]=16'hC987;
        rom[1164]=16'hCD00;
        rom[1165]=16'hD072;
        rom[1166]=16'hD3DD;
        rom[1167]=16'hD740;
        rom[1168]=16'hDA9B;
        rom[1169]=16'hDDEE;
        rom[1170]=16'hE137;
        rom[1171]=16'hE476;
        rom[1172]=16'hE7AC;
        rom[1173]=16'hEAD6;
        rom[1174]=16'hEDF6;
        rom[1175]=16'hF10A;
        rom[1176]=16'hF411;
        rom[1177]=16'hF70C;
        rom[1178]=16'hF9FA;
        rom[1179]=16'hFCDA;
        rom[1180]=16'hFFAD;
        rom[1181]=16'h0271;
        rom[1182]=16'h0526;
        rom[1183]=16'h07CC;
        rom[1184]=16'h0A62;
        rom[1185]=16'h0CE8;
        rom[1186]=16'h0F5E;
        rom[1187]=16'h11C3;
        rom[1188]=16'h1417;
        rom[1189]=16'h1659;
        rom[1190]=16'h1889;
        rom[1191]=16'h1AA7;
        rom[1192]=16'h1CB3;
        rom[1193]=16'h1EAB;
        rom[1194]=16'h2091;
        rom[1195]=16'h2263;
        rom[1196]=16'h2421;
        rom[1197]=16'h25CB;
        rom[1198]=16'h2761;
        rom[1199]=16'h28E2;
        rom[1200]=16'h2A4F;
        rom[1201]=16'h2BA6;
        rom[1202]=16'h2CE8;
        rom[1203]=16'h2E15;
        rom[1204]=16'h2F2D;
        rom[1205]=16'h302F;
        rom[1206]=16'h311A;
        rom[1207]=16'h31F0;
        rom[1208]=16'h32B0;
        rom[1209]=16'h3359;
        rom[1210]=16'h33EC;
        rom[1211]=16'h3469;
        rom[1212]=16'h34CF;
        rom[1213]=16'h351E;
        rom[1214]=16'h3557;
        rom[1215]=16'h3579;
        rom[1216]=16'h3584;
        rom[1217]=16'h3579;
        rom[1218]=16'h3557;
        rom[1219]=16'h351E;
        rom[1220]=16'h34CF;
        rom[1221]=16'h3469;
        rom[1222]=16'h33EC;
        rom[1223]=16'h3359;
        rom[1224]=16'h32B0;
        rom[1225]=16'h31F0;
        rom[1226]=16'h311A;
        rom[1227]=16'h302F;
        rom[1228]=16'h2F2D;
        rom[1229]=16'h2E15;
        rom[1230]=16'h2CE8;
        rom[1231]=16'h2BA6;
        rom[1232]=16'h2A4F;
        rom[1233]=16'h28E2;
        rom[1234]=16'h2761;
        rom[1235]=16'h25CB;
        rom[1236]=16'h2421;
        rom[1237]=16'h2263;
        rom[1238]=16'h2091;
        rom[1239]=16'h1EAB;
        rom[1240]=16'h1CB3;
        rom[1241]=16'h1AA7;
        rom[1242]=16'h1889;
        rom[1243]=16'h1659;
        rom[1244]=16'h1417;
        rom[1245]=16'h11C3;
        rom[1246]=16'h0F5E;
        rom[1247]=16'h0CE8;
        rom[1248]=16'h0A62;
        rom[1249]=16'h07CC;
        rom[1250]=16'h0526;
        rom[1251]=16'h0271;
        rom[1252]=16'hFFAD;
        rom[1253]=16'hFCDA;
        rom[1254]=16'hF9FA;
        rom[1255]=16'hF70C;
        rom[1256]=16'hF411;
        rom[1257]=16'hF10A;
        rom[1258]=16'hEDF6;
        rom[1259]=16'hEAD6;
        rom[1260]=16'hE7AC;
        rom[1261]=16'hE476;
        rom[1262]=16'hE137;
        rom[1263]=16'hDDEE;
        rom[1264]=16'hDA9B;
        rom[1265]=16'hD740;
        rom[1266]=16'hD3DD;
        rom[1267]=16'hD072;
        rom[1268]=16'hCD00;
        rom[1269]=16'hC987;
        rom[1270]=16'hC608;
        rom[1271]=16'hC284;
        rom[1272]=16'hBEFB;
        rom[1273]=16'hBB6D;
        rom[1274]=16'hB7DC;
        rom[1275]=16'hB447;
        rom[1276]=16'hB0AF;
        rom[1277]=16'hAD15;
        rom[1278]=16'hA97A;
        rom[1279]=16'hA5DD;
        // table 5: Fold
        rom[1280]=16'h0000;
        rom[1281]=16'h0603;
        rom[1282]=16'h0C05;
        rom[1283]=16'h1206;
        rom[1284]=16'h1803;
        rom[1285]=16'h1DFD;
        rom[1286]=16'h23F2;
        rom[1287]=16'h29E2;
        rom[1288]=16'h2FCB;
        rom[1289]=16'h35AD;
        rom[1290]=16'h3B87;
        rom[1291]=16'h4157;
        rom[1292]=16'h471D;
        rom[1293]=16'h4CD9;
        rom[1294]=16'h5288;
        rom[1295]=16'h582B;
        rom[1296]=16'h5DC0;
        rom[1297]=16'h592C;
        rom[1298]=16'h53B4;
        rom[1299]=16'h4E4D;
        rom[1300]=16'h48F7;
        rom[1301]=16'h43B2;
        rom[1302]=16'h3E80;
        rom[1303]=16'h3962;
        rom[1304]=16'h3458;
        rom[1305]=16'h2F63;
        rom[1306]=16'h2A83;
        rom[1307]=16'h25BA;
        rom[1308]=16'h2108;
        rom[1309]=16'h1C6F;
        rom[1310]=16'h17ED;
        rom[1311]=16'h1386;
        rom[1312]=16'h0F38;
        rom[1313]=16'h0B05;
        rom[1314]=16'h06EE;
        rom[1315]=16'h02F2;
        rom[1316]=16'hFF13;
        rom[1317]=16'hFB51;
        rom[1318]=16'hF7AD;
        rom[1319]=16'hF427;
        rom[1320]=16'hF0C1;
        rom[1321]=16'hED79;
        rom[1322]=16'hEA52;
        rom[1323]=16'hE74B;
        rom[1324]=16'hE465;
        rom[1325]=16'hE1A0;
        rom[1326]=16'hDEFD;
        rom[1327]=16'hDC7C;
        rom[1328]=16'hDA1D;
        rom[1329]=16'hD7E2;
        rom[1330]=16'hD5C9;
        rom[1331]=16'hD3D5;
        rom[1332]=16'hD204;
        rom[1333]=16'hD057;
        rom[1334]=16'hCECF;
        rom[1335]=16'hCD6B;
        rom[1336]=16'hCC2C;
        rom[1337]=16'hCB13;
        rom[1338]=16'hCA1E;
        rom[1339]=16'hC94F;
        rom[1340]=16'hC8A5;
        rom[1341]=16'hC821;
        rom[1342]=16'hC7C3;
        rom[1343]=16'hC78A;
        rom[1344]=16'hC777;
        rom[1345]=16'hC78A;
        rom[1346]=16'hC7C3;
        rom[1347]=16'hC821;
        rom[1348]=16'hC8A5;
        rom[1349]=16'hC94F;
        rom[1350]=16'hCA1E;
        rom[1351]=16'hCB13;
        rom[1352]=16'hCC2C;
        rom[1353]=16'hCD6B;
        rom[1354]=16'hCECF;
        rom[1355]=16'hD057;
        rom[1356]=16'hD204;
        rom[1357]=16'hD3D5;
        rom[1358]=16'hD5C9;
        rom[1359]=16'hD7E2;
        rom[1360]=16'hDA1D;
        rom[1361]=16'hDC7C;
        rom[1362]=16'hDEFD;
        rom[1363]=16'hE1A0;
        rom[1364]=16'hE465;
        rom[1365]=16'hE74B;
        rom[1366]=16'hEA52;
        rom[1367]=16'hED79;
        rom[1368]=16'hF0C1;
        rom[1369]=16'hF427;
        rom[1370]=16'hF7AD;
        rom[1371]=16'hFB51;
        rom[1372]=16'hFF13;
        rom[1373]=16'h02F2;
        rom[1374]=16'h06EE;
        rom[1375]=16'h0B05;
        rom[1376]=16'h0F38;
        rom[1377]=16'h1386;
        rom[1378]=16'h17ED;
        rom[1379]=16'h1C6F;
        rom[1380]=16'h2108;
        rom[1381]=16'h25BA;
        rom[1382]=16'h2A83;
        rom[1383]=16'h2F63;
        rom[1384]=16'h3458;
        rom[1385]=16'h3962;
        rom[1386]=16'h3E80;
        rom[1387]=16'h43B2;
        rom[1388]=16'h48F7;
        rom[1389]=16'h4E4D;
        rom[1390]=16'h53B4;
        rom[1391]=16'h592C;
        rom[1392]=16'h5DC0;
        rom[1393]=16'h582B;
        rom[1394]=16'h5288;
        rom[1395]=16'h4CD9;
        rom[1396]=16'h471D;
        rom[1397]=16'h4157;
        rom[1398]=16'h3B87;
        rom[1399]=16'h35AD;
        rom[1400]=16'h2FCB;
        rom[1401]=16'h29E2;
        rom[1402]=16'h23F2;
        rom[1403]=16'h1DFD;
        rom[1404]=16'h1803;
        rom[1405]=16'h1206;
        rom[1406]=16'h0C05;
        rom[1407]=16'h0603;
        rom[1408]=16'h0000;
        rom[1409]=16'hF9FD;
        rom[1410]=16'hF3FB;
        rom[1411]=16'hEDFA;
        rom[1412]=16'hE7FD;
        rom[1413]=16'hE203;
        rom[1414]=16'hDC0E;
        rom[1415]=16'hD61E;
        rom[1416]=16'hD035;
        rom[1417]=16'hCA53;
        rom[1418]=16'hC479;
        rom[1419]=16'hBEA9;
        rom[1420]=16'hB8E3;
        rom[1421]=16'hB327;
        rom[1422]=16'hAD78;
        rom[1423]=16'hA7D5;
        rom[1424]=16'hA240;
        rom[1425]=16'hA6D4;
        rom[1426]=16'hAC4C;
        rom[1427]=16'hB1B3;
        rom[1428]=16'hB709;
        rom[1429]=16'hBC4E;
        rom[1430]=16'hC180;
        rom[1431]=16'hC69E;
        rom[1432]=16'hCBA8;
        rom[1433]=16'hD09D;
        rom[1434]=16'hD57D;
        rom[1435]=16'hDA46;
        rom[1436]=16'hDEF8;
        rom[1437]=16'hE391;
        rom[1438]=16'hE813;
        rom[1439]=16'hEC7A;
        rom[1440]=16'hF0C8;
        rom[1441]=16'hF4FB;
        rom[1442]=16'hF912;
        rom[1443]=16'hFD0E;
        rom[1444]=16'h00ED;
        rom[1445]=16'h04AF;
        rom[1446]=16'h0853;
        rom[1447]=16'h0BD9;
        rom[1448]=16'h0F3F;
        rom[1449]=16'h1287;
        rom[1450]=16'h15AE;
        rom[1451]=16'h18B5;
        rom[1452]=16'h1B9B;
        rom[1453]=16'h1E60;
        rom[1454]=16'h2103;
        rom[1455]=16'h2384;
        rom[1456]=16'h25E3;
        rom[1457]=16'h281E;
        rom[1458]=16'h2A37;
        rom[1459]=16'h2C2B;
        rom[1460]=16'h2DFC;
        rom[1461]=16'h2FA9;
        rom[1462]=16'h3131;
        rom[1463]=16'h3295;
        rom[1464]=16'h33D4;
        rom[1465]=16'h34ED;
        rom[1466]=16'h35E2;
        rom[1467]=16'h36B1;
        rom[1468]=16'h375B;
        rom[1469]=16'h37DF;
        rom[1470]=16'h383D;
        rom[1471]=16'h3876;
        rom[1472]=16'h3889;
        rom[1473]=16'h3876;
        rom[1474]=16'h383D;
        rom[1475]=16'h37DF;
        rom[1476]=16'h375B;
        rom[1477]=16'h36B1;
        rom[1478]=16'h35E2;
        rom[1479]=16'h34ED;
        rom[1480]=16'h33D4;
        rom[1481]=16'h3295;
        rom[1482]=16'h3131;
        rom[1483]=16'h2FA9;
        rom[1484]=16'h2DFC;
        rom[1485]=16'h2C2B;
        rom[1486]=16'h2A37;
        rom[1487]=16'h281E;
        rom[1488]=16'h25E3;
        rom[1489]=16'h2384;
        rom[1490]=16'h2103;
        rom[1491]=16'h1E60;
        rom[1492]=16'h1B9B;
        rom[1493]=16'h18B5;
        rom[1494]=16'h15AE;
        rom[1495]=16'h1287;
        rom[1496]=16'h0F3F;
        rom[1497]=16'h0BD9;
        rom[1498]=16'h0853;
        rom[1499]=16'h04AF;
        rom[1500]=16'h00ED;
        rom[1501]=16'hFD0E;
        rom[1502]=16'hF912;
        rom[1503]=16'hF4FB;
        rom[1504]=16'hF0C8;
        rom[1505]=16'hEC7A;
        rom[1506]=16'hE813;
        rom[1507]=16'hE391;
        rom[1508]=16'hDEF8;
        rom[1509]=16'hDA46;
        rom[1510]=16'hD57D;
        rom[1511]=16'hD09D;
        rom[1512]=16'hCBA8;
        rom[1513]=16'hC69E;
        rom[1514]=16'hC180;
        rom[1515]=16'hBC4E;
        rom[1516]=16'hB709;
        rom[1517]=16'hB1B3;
        rom[1518]=16'hAC4C;
        rom[1519]=16'hA6D4;
        rom[1520]=16'hA240;
        rom[1521]=16'hA7D5;
        rom[1522]=16'hAD78;
        rom[1523]=16'hB327;
        rom[1524]=16'hB8E3;
        rom[1525]=16'hBEA9;
        rom[1526]=16'hC479;
        rom[1527]=16'hCA53;
        rom[1528]=16'hD035;
        rom[1529]=16'hD61E;
        rom[1530]=16'hDC0E;
        rom[1531]=16'hE203;
        rom[1532]=16'hE7FD;
        rom[1533]=16'hEDFA;
        rom[1534]=16'hF3FB;
        rom[1535]=16'hF9FD;
        // table 6: Bell
        rom[1536]=16'h0000;
        rom[1537]=16'h36DE;
        rom[1538]=16'h58D9;
        rom[1539]=16'h59EC;
        rom[1540]=16'h3B55;
        rom[1541]=16'h09B8;
        rom[1542]=16'hD6B8;
        rom[1543]=16'hB19A;
        rom[1544]=16'hA283;
        rom[1545]=16'hA98B;
        rom[1546]=16'hC0F8;
        rom[1547]=16'hE0BC;
        rom[1548]=16'h0173;
        rom[1549]=16'h1E14;
        rom[1550]=16'h3445;
        rom[1551]=16'h43C6;
        rom[1552]=16'h4D9A;
        rom[1553]=16'h5330;
        rom[1554]=16'h55D3;
        rom[1555]=16'h5653;
        rom[1556]=16'h54DF;
        rom[1557]=16'h50FD;
        rom[1558]=16'h49A5;
        rom[1559]=16'h3D7A;
        rom[1560]=16'h2B3D;
        rom[1561]=16'h1271;
        rom[1562]=16'hF429;
        rom[1563]=16'hD3B8;
        rom[1564]=16'hB6D9;
        rom[1565]=16'hA4E3;
        rom[1566]=16'hA4BD;
        rom[1567]=16'hB9FF;
        rom[1568]=16'hE247;
        rom[1569]=16'h143E;
        rom[1570]=16'h417F;
        rom[1571]=16'h5B48;
        rom[1572]=16'h5845;
        rom[1573]=16'h38C6;
        rom[1574]=16'h0719;
        rom[1575]=16'hD3AA;
        rom[1576]=16'hAEAA;
        rom[1577]=16'hA245;
        rom[1578]=16'hAFDC;
        rom[1579]=16'hD105;
        rom[1580]=16'hFB2A;
        rom[1581]=16'h23B8;
        rom[1582]=16'h4333;
        rom[1583]=16'h5653;
        rom[1584]=16'h5D86;
        rom[1585]=16'h5B8C;
        rom[1586]=16'h5404;
        rom[1587]=16'h4A58;
        rom[1588]=16'h4137;
        rom[1589]=16'h3A6F;
        rom[1590]=16'h370C;
        rom[1591]=16'h3782;
        rom[1592]=16'h3BC7;
        rom[1593]=16'h4349;
        rom[1594]=16'h4CD2;
        rom[1595]=16'h5652;
        rom[1596]=16'h5CCD;
        rom[1597]=16'h5C88;
        rom[1598]=16'h51C7;
        rom[1599]=16'h3A19;
        rom[1600]=16'h160C;
        rom[1601]=16'hEA9E;
        rom[1602]=16'hC16C;
        rom[1603]=16'hA6B3;
        rom[1604]=16'hA516;
        rom[1605]=16'hC068;
        rom[1606]=16'hF217;
        rom[1607]=16'h29BC;
        rom[1608]=16'h52BC;
        rom[1609]=16'h5CE7;
        rom[1610]=16'h43EF;
        rom[1611]=16'h1199;
        rom[1612]=16'hD961;
        rom[1613]=16'hAFD8;
        rom[1614]=16'hA251;
        rom[1615]=16'hB2B8;
        rom[1616]=16'hD8DB;
        rom[1617]=16'h0763;
        rom[1618]=16'h317F;
        rom[1619]=16'h4EC9;
        rom[1620]=16'h5C68;
        rom[1621]=16'h5C0A;
        rom[1622]=16'h51DB;
        rom[1623]=16'h4298;
        rom[1624]=16'h324E;
        rom[1625]=16'h23D5;
        rom[1626]=16'h18DF;
        rom[1627]=16'h1243;
        rom[1628]=16'h1057;
        rom[1629]=16'h132B;
        rom[1630]=16'h1A9C;
        rom[1631]=16'h263A;
        rom[1632]=16'h350C;
        rom[1633]=16'h4538;
        rom[1634]=16'h53CA;
        rom[1635]=16'h5CC0;
        rom[1636]=16'h5BA3;
        rom[1637]=16'h4CCD;
        rom[1638]=16'h2F25;
        rom[1639]=16'h05D1;
        rom[1640]=16'hD8D8;
        rom[1641]=16'hB3D7;
        rom[1642]=16'hA295;
        rom[1643]=16'hAC5C;
        rom[1644]=16'hD01A;
        rom[1645]=16'h037A;
        rom[1646]=16'h35FC;
        rom[1647]=16'h56FF;
        rom[1648]=16'h5C1D;
        rom[1649]=16'h44CB;
        rom[1650]=16'h19CB;
        rom[1651]=16'hE901;
        rom[1652]=16'hBFFB;
        rom[1653]=16'hA7AB;
        rom[1654]=16'hA2C3;
        rom[1655]=16'hAE93;
        rom[1656]=16'hC55B;
        rom[1657]=16'hE0CD;
        rom[1658]=16'hFBC1;
        rom[1659]=16'h12F8;
        rom[1660]=16'h2503;
        rom[1661]=16'h31BF;
        rom[1662]=16'h39B2;
        rom[1663]=16'h3D82;
        rom[1664]=16'h3D99;
        rom[1665]=16'h39F6;
        rom[1666]=16'h322C;
        rom[1667]=16'h258C;
        rom[1668]=16'h137E;
        rom[1669]=16'hFC17;
        rom[1670]=16'hE0C0;
        rom[1671]=16'hC4D7;
        rom[1672]=16'hADD4;
        rom[1673]=16'hA285;
        rom[1674]=16'hA921;
        rom[1675]=16'hC465;
        rom[1676]=16'hF0D2;
        rom[1677]=16'h23AD;
        rom[1678]=16'h4D1F;
        rom[1679]=16'h5DC0;
        rom[1680]=16'h4D7E;
        rom[1681]=16'h2087;
        rom[1682]=16'hE6FE;
        rom[1683]=16'hB6D1;
        rom[1684]=16'hA260;
        rom[1685]=16'hB0AB;
        rom[1686]=16'hDAFC;
        rom[1687]=16'h10DD;
        rom[1688]=16'h3FB8;
        rom[1689]=16'h5A11;
        rom[1690]=16'h5B3C;
        rom[1691]=16'h46D3;
        rom[1692]=16'h2550;
        rom[1693]=16'h000D;
        rom[1694]=16'hDE5A;
        rom[1695]=16'hC43D;
        rom[1696]=16'hB2B2;
        rom[1697]=16'hA89F;
        rom[1698]=16'hA3ED;
        rom[1699]=16'hA268;
        rom[1700]=16'hA244;
        rom[1701]=16'hA25C;
        rom[1702]=16'hA247;
        rom[1703]=16'hA25B;
        rom[1704]=16'hA3A8;
        rom[1705]=16'hA7DF;
        rom[1706]=16'hB119;
        rom[1707]=16'hC15C;
        rom[1708]=16'hD9D7;
        rom[1709]=16'hF9E3;
        rom[1710]=16'h1E26;
        rom[1711]=16'h404B;
        rom[1712]=16'h57EB;
        rom[1713]=16'h5CE9;
        rom[1714]=16'h4AB9;
        rom[1715]=16'h2369;
        rom[1716]=16'hF0A7;
        rom[1717]=16'hC190;
        rom[1718]=16'hA5A1;
        rom[1719]=16'hA69F;
        rom[1720]=16'hC471;
        rom[1721]=16'hF4FD;
        rom[1722]=16'h283A;
        rom[1723]=16'h4E6D;
        rom[1724]=16'h5DA3;
        rom[1725]=16'h5424;
        rom[1726]=16'h3770;
        rom[1727]=16'h10E1;
        rom[1728]=16'hE9F4;
        rom[1729]=16'hC995;
        rom[1730]=16'hB31C;
        rom[1731]=16'hA6AF;
        rom[1732]=16'hA261;
        rom[1733]=16'hA360;
        rom[1734]=16'hA6E3;
        rom[1735]=16'hAAA7;
        rom[1736]=16'hAD22;
        rom[1737]=16'hAD84;
        rom[1738]=16'hABAD;
        rom[1739]=16'hA830;
        rom[1740]=16'hA45B;
        rom[1741]=16'hA242;
        rom[1742]=16'hA4A8;
        rom[1743]=16'hAE95;
        rom[1744]=16'hC285;
        rom[1745]=16'hE121;
        rom[1746]=16'h07E8;
        rom[1747]=16'h3059;
        rom[1748]=16'h508A;
        rom[1749]=16'h5DBF;
        rom[1750]=16'h50B0;
        rom[1751]=16'h29F4;
        rom[1752]=16'hF40C;
        rom[1753]=16'hC128;
        rom[1754]=16'hA47B;
        rom[1755]=16'hA9D5;
        rom[1756]=16'hCFCA;
        rom[1757]=16'h07C7;
        rom[1758]=16'h3C58;
        rom[1759]=16'h5A71;
        rom[1760]=16'h58EB;
        rom[1761]=16'h3ADB;
        rom[1762]=16'h0C6D;
        rom[1763]=16'hDCC5;
        rom[1764]=16'hB837;
        rom[1765]=16'hA514;
        rom[1766]=16'hA390;
        rom[1767]=16'hAFA9;
        rom[1768]=16'hC3B0;
        rom[1769]=16'hDA4B;
        rom[1770]=16'hEF8B;
        rom[1771]=16'h011F;
        rom[1772]=16'h0E07;
        rom[1773]=16'h160A;
        rom[1774]=16'h1945;
        rom[1775]=16'h17D3;
        rom[1776]=16'h11AC;
        rom[1777]=16'h06B7;
        rom[1778]=16'hF707;
        rom[1779]=16'hE343;
        rom[1780]=16'hCD1F;
        rom[1781]=16'hB7BE;
        rom[1782]=16'hA7B2;
        rom[1783]=16'hA257;
        rom[1784]=16'hAC53;
        rom[1785]=16'hC781;
        rom[1786]=16'hF0EE;
        rom[1787]=16'h2016;
        rom[1788]=16'h485A;
        rom[1789]=16'h5CD8;
        rom[1790]=16'h557C;
        rom[1791]=16'h3312;
    end

    always @(posedge clk) begin
        sample_a <= rom[{sel_a, phase_a}];
        sample_b <= rom[{sel_b, phase_b}];
    end

endmodule
